killee/Sauna-controller/images/IMG_20210213_231534.jpg

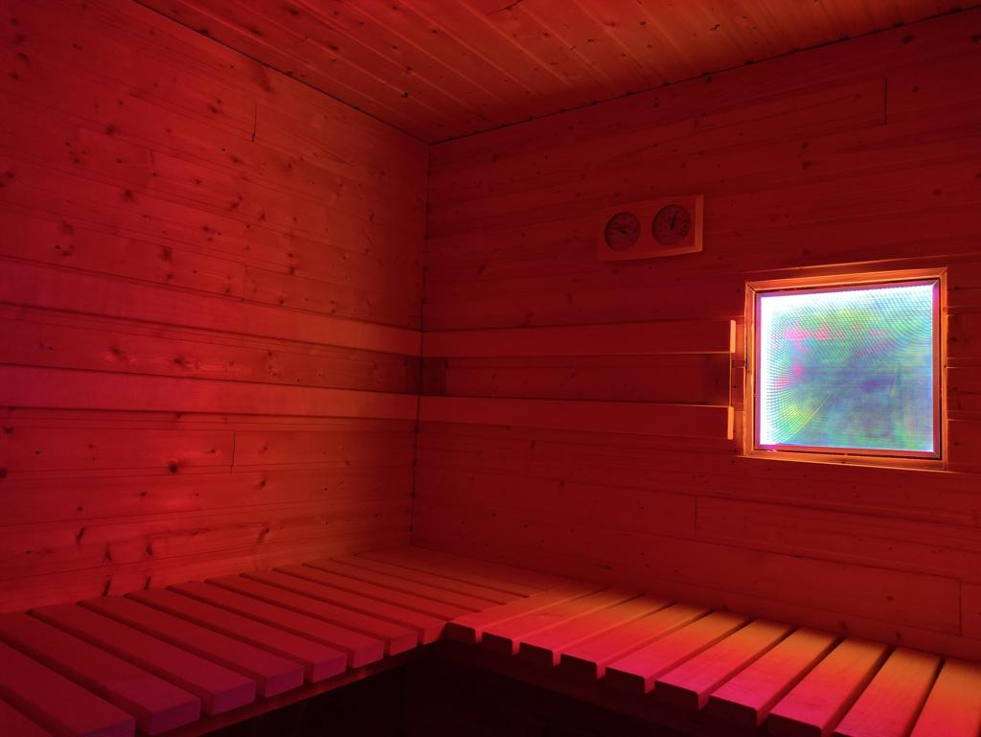
images/IMG_20210213_231534.jpg
