killee/Sauna-controller/images/IMG_20210213_231546.jpg

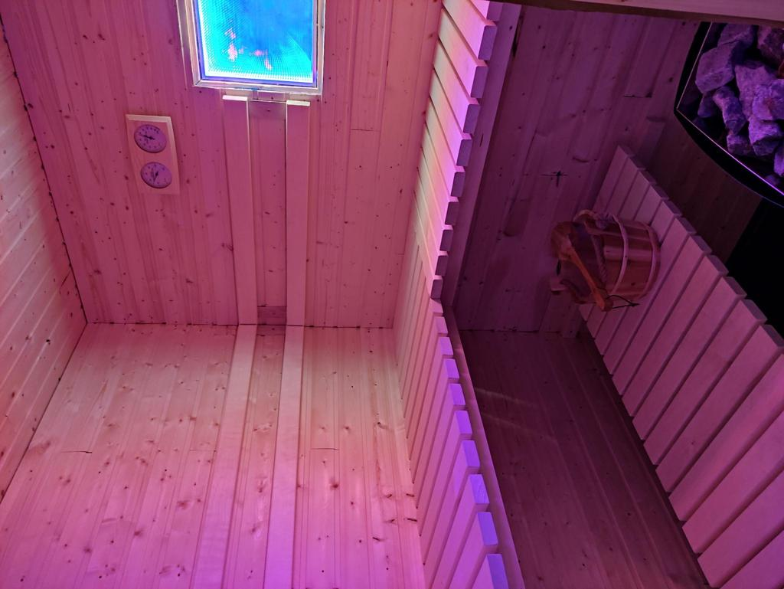
images/IMG_20210213_231546.jpg
