killee/Sauna-controller/images/IMG_20210215_231151_1.jpg

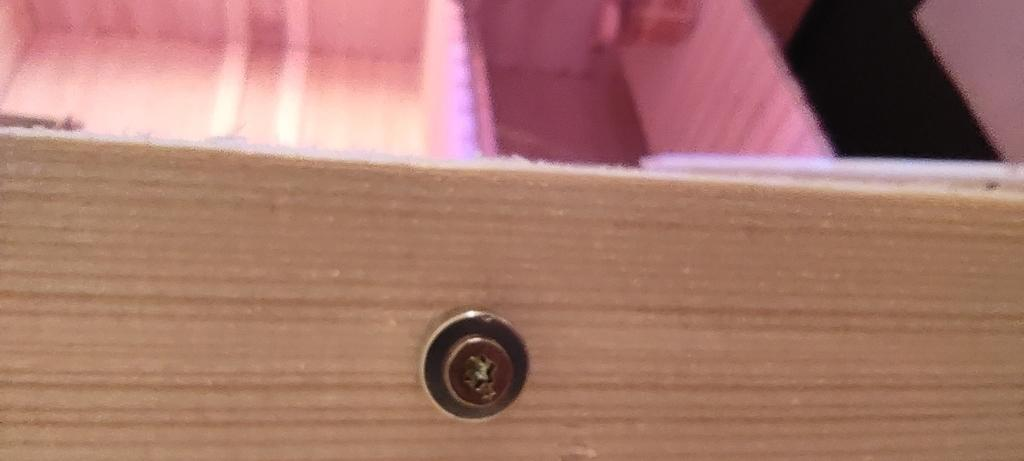
images/IMG_20210215_231151_1.jpg
