killee/Sauna-controller/images/IMG_20210215_233316.jpg

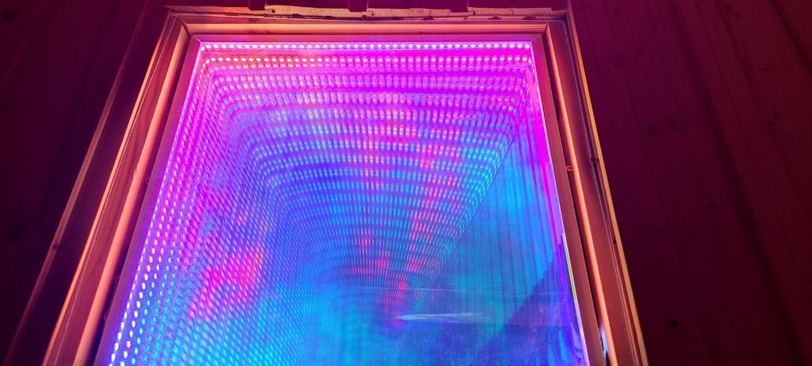
images/IMG_20210215_233316.jpg
